m0hammedbshaheer/Orchard_Eye/ML_model/Database_for_model/Raw_images_medium/img_20260325_164936.jpg

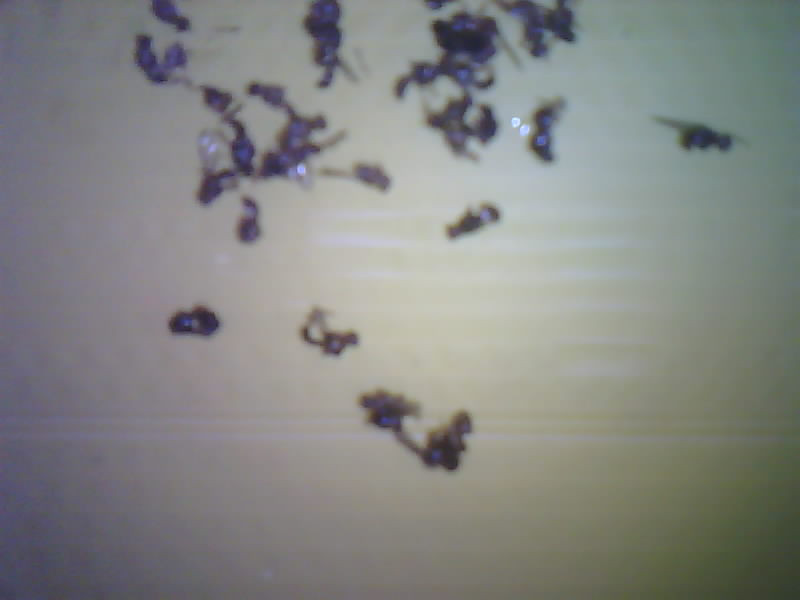
ML_model/Database_for_model/Raw_images_medium/img_20260325_164936.jpg
