m0hammedbshaheer/Orchard_Eye/webapp/frontend/Assets/OrchardEye.png

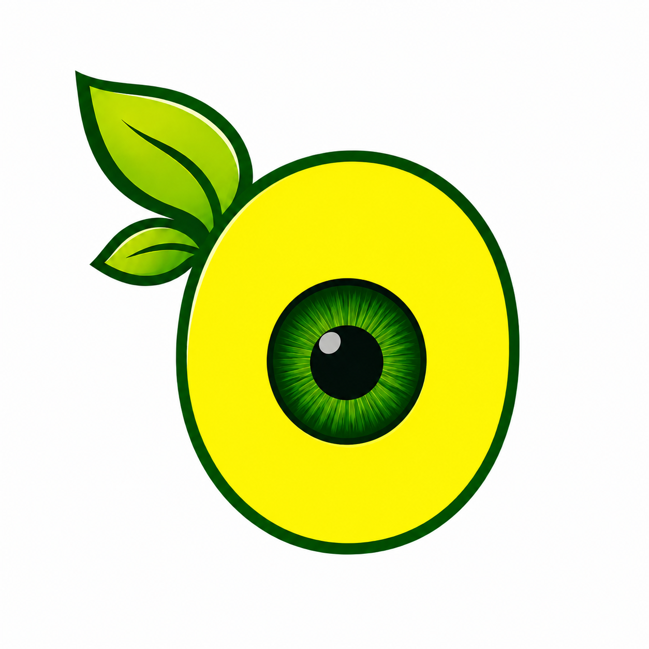
webapp/frontend/Assets/OrchardEye.png
